acidbourbon/midi2cv/PCB/project.sch

## KiCad design PCB/project.sch (2016-03-10)

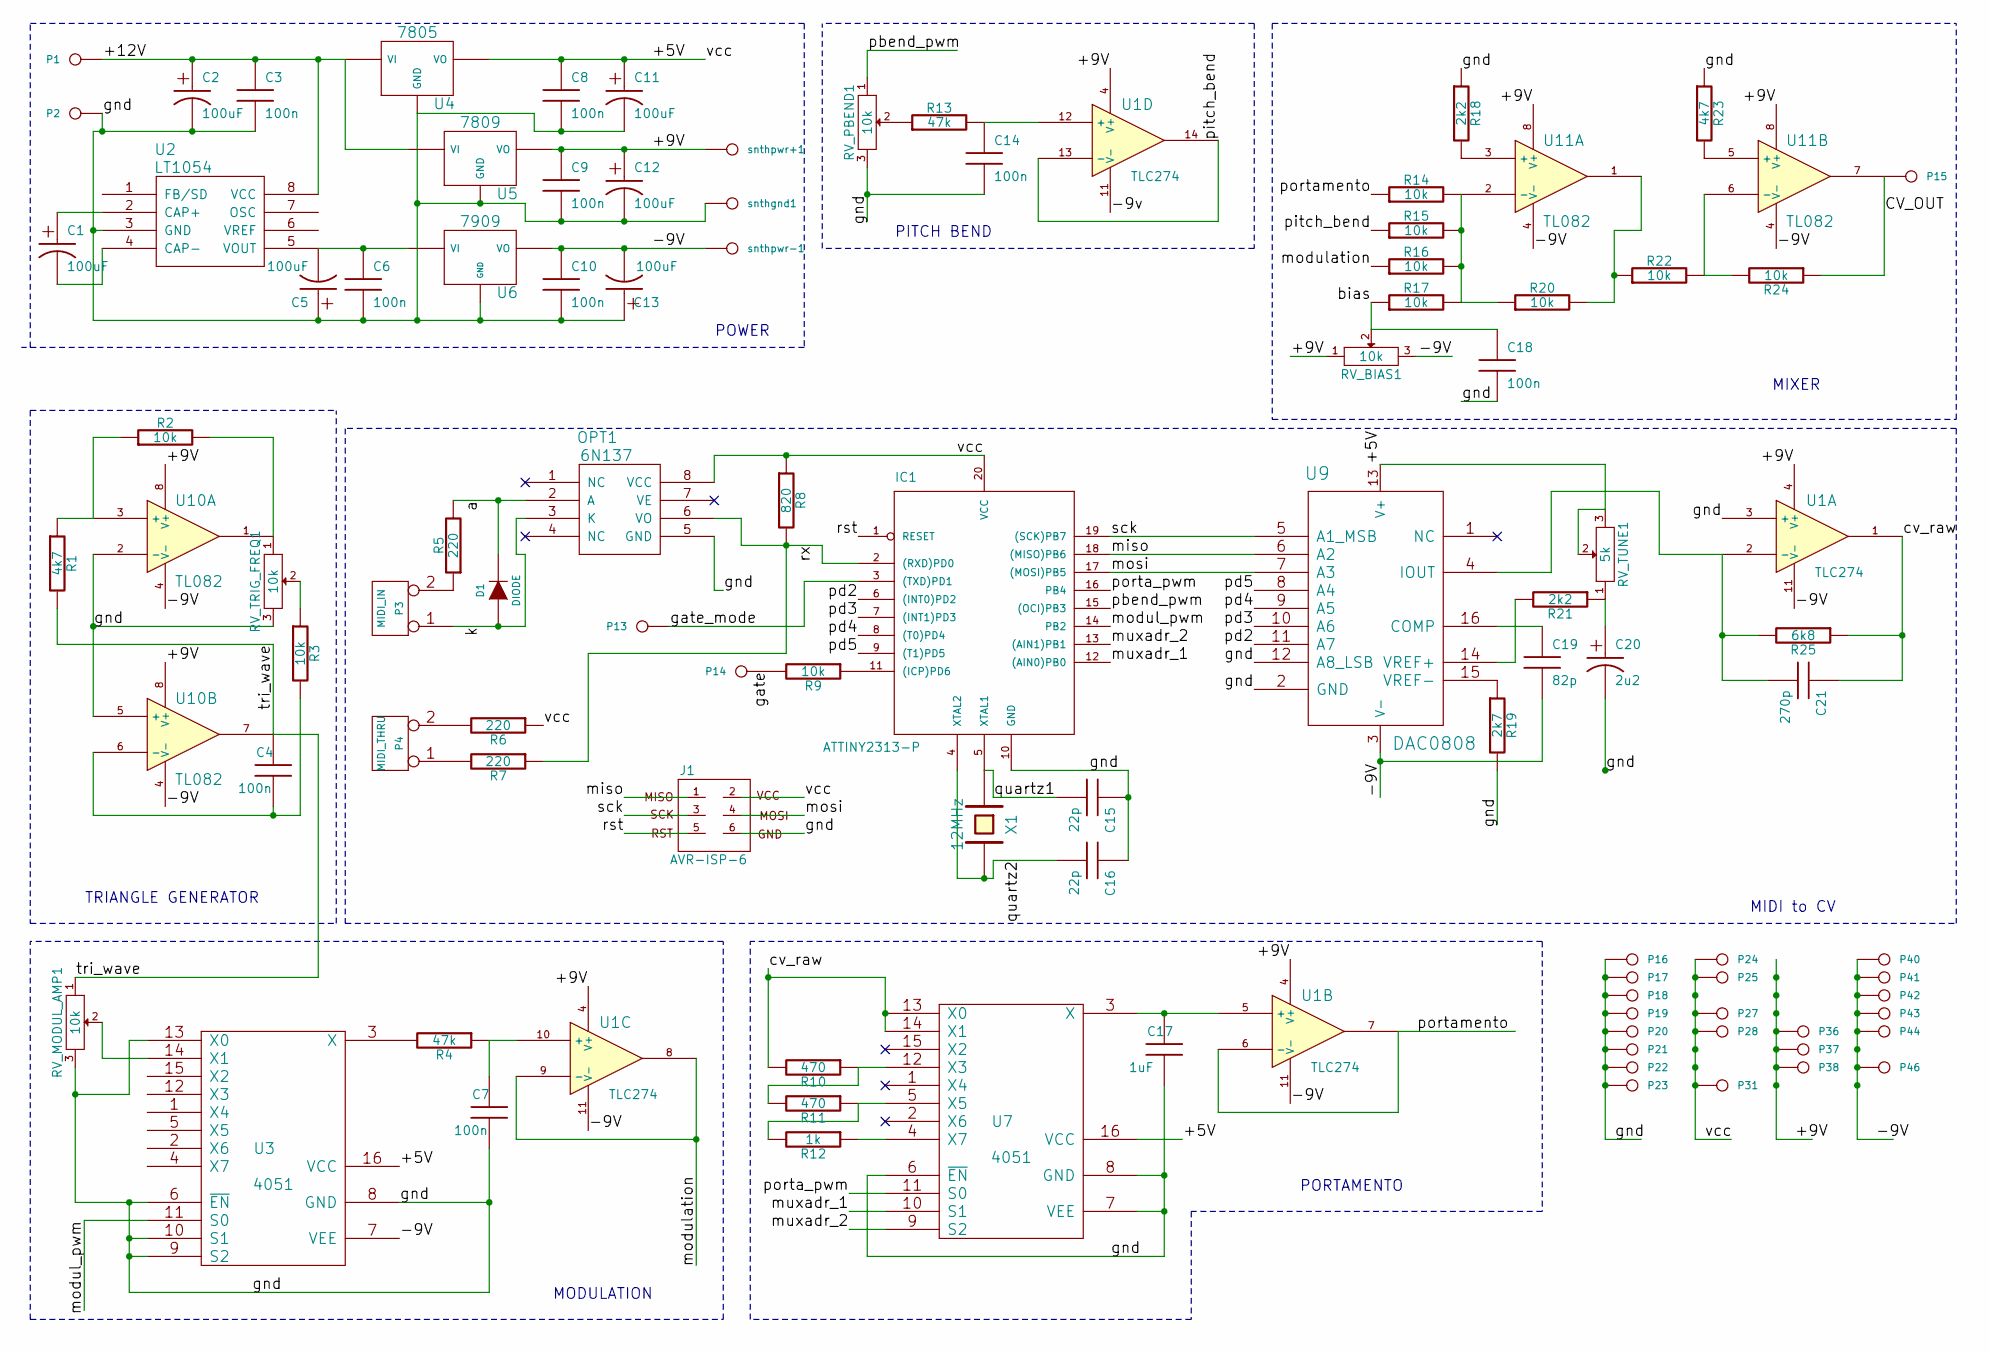
[picture p4: schematic project.sch]

Parts:
C1, C2, C5, C11, C12, C13: 100uF
C3, C4, C6, C7, C8, C9, C10, C14, C18: 100n
C15, C16: 22p
C17: 1uF
C19: 82p
C20: 2u2
C21: 270p
D1: DIODE
IC1: ATTINY2313-P; DIL20
J1: AVR-ISP-6
OPT1: 6N137
P1, P2, P13, P14, P15, P16, P17, P18, P19, P20, P21, P22, P23, P24, P25, P27, P28, P31, P36, P37, P38, P40, P41, P42, P43, P44, P46: CONN_1
P3: MIDI_IN
P4: MIDI_THRU
R1, R23: 4k7
R2, R3, R9, R14, R15, R16, R17, R20, R22, R24: 10k
R4, R13: 47k
R5, R6, R7: 220
R8: 820
R10, R11: 470
R12: 1k
R18, R21: 2k2
R19: 2k7
R25: 6k8
RV_BIAS1: 10k
RV_MODUL_AMP1: 10k
RV_PBEND1: 10k
RV_TRIG_FREQ1: 10k
RV_TUNE1: 5k
U1: TLC274
U2: LT1054
U3, U7: 4051
U4: 7805
U5: 7809
U6: 7909
U9: DAC0808
U10, U11: TL082
X1: 12MHz
snthgnd1: CONN_1
snthpwr+1: CONN_1
snthpwr-1: CONN_1

Connections:
+5V: C8.1, C11.1, IC1.20 (VCC), J1.2, OPT1.8 (VCC), P24.1, P25.1, P27.1, P28.1, P31.1, R6.1, R8.1, RV_TUNE1.2, RV_TUNE1.3, U3.16 (VCC), U4.VO, U7.16 (VCC), U9.13 (V+)
+9V: C9.1, C12.1, P36.1, P37.1, P38.1, RV_BIAS1.1, U1.4 (V+), U5.VO, U10.8 (V+), U11.8 (V+), snthpwr+1.1
+12V: C2.1, C3.1, P1.1, U2.8 (VCC), U4.VI, U5.VI
-9V: C10.1, C13.2, C19.2, P40.1, P41.1, P42.1, P43.1, P44.1, P46.1, RV_BIAS1.3, U1.11 (V-), U3.7 (VEE), U6.VO, U9.3 (V-), U10.4 (V-), U11.4 (V-), snthpwr-1.1
CV_OUT: P15.1, R24.1, U11.7
unnamed: C1.1, U2.2 (CAP+)
unnamed: C1.2, U2.4 (CAP-)
unnamed: C4.2, R3.2, U10.6 (-)
unnamed: C5.2, C6.1, U2.5 (VOUT), U6.VI
unnamed: C7.1, R4.1, U1.10 (+)
unnamed: C14.1, R13.2, U1.12 (+)
unnamed: C17.1, U1.5 (+), U7.3 (X)
unnamed: C19.1, U9.16 (COMP)
unnamed: C20.1, R21.1, RV_TUNE1.1
unnamed: C21.2, R25.2, U1.2 (-), U9.4 (IOUT)
unnamed: IC1.11 ((ICP)PD6), R9.1
unnamed: P3.2 (PM), R5.1
unnamed: P4.1, R7.2
unnamed: P4.2 (PM), R6.2
unnamed: R1.1, R2.1, U10.3 (+)
unnamed: R2.2, RV_TRIG_FREQ1.1, U10.1
unnamed: R3.1, RV_TRIG_FREQ1.2
unnamed: R4.2, U3.3 (X)
unnamed: R10.1, R11.2, U7.12 (X3)
unnamed: R11.1, R12.2, U7.5 (X5)
unnamed: R12.1, U7.4 (X7)
unnamed: R13.1, RV_PBEND1.2
unnamed: R14.2, R15.2, R16.2, R17.2, R20.1, U11.2 (-)
unnamed: R18.2, U11.3 (+)
unnamed: R19.1, U9.15 (VREF-)
unnamed: R20.2, R22.1, U11.1
unnamed: R21.2, U9.14 (VREF+)
unnamed: R22.2, R24.2, U11.6 (-)
unnamed: R23.2, U11.5 (+)
unnamed: RV_MODUL_AMP1.2, U3.14 (X1)
a: D1.2 (K), OPT1.2 (A), R5.2
bias: C18.1, R17.1, RV_BIAS1.2
cv_raw: C21.1, R10.2, R25.1, U1.1, U7.13 (X0), U7.14 (X1)
gate: P14.1, R9.2
gate_mode: IC1.3 ((TXD)PD1), P13.1
gnd: C2.2, C3.2, C5.1, C6.2, C7.2, C8.2, C9.2, C10.2, C11.2, C12.2, C13.1, C14.2, C15.1, C16.1, C17.2, C18.2, C20.2, IC1.10 (GND), J1.6, OPT1.5 (GND), P2.1, P16.1, P17.1, P18.1, P19.1, P20.1, P21.1, P22.1, P23.1, R18.1, R19.2, R23.1, RV_MODUL_AMP1.3, RV_PBEND1.3, RV_TRIG_FREQ1.3, U1.3 (+), U2.3 (GND), U3.6 (~EN), U3.8 (GND), U3.9 (S2), U3.10 (S1), U3.13 (X0), U4.GND, U5.GND, U6.GND, U7.6 (~EN), U7.7 (VEE), U7.8 (GND), U9.2 (GND), U9.12 (A8_LSB), U10.2 (-), U10.5 (+), snthgnd1.1
k: D1.1 (A), OPT1.3 (K), P3.1
miso: IC1.18 ((MISO)PB6), J1.1, U9.6 (A2)
modul_pwm: IC1.14 (PB2), U3.11 (S0)
modulation: R16.1, U1.8, U1.9 (-)
mosi: IC1.17 ((MOSI)PB5), J1.4, U9.7 (A3)
muxadr_1: IC1.12 ((AIN0)PB0), U7.10 (S1)
muxadr_2: IC1.13 ((AIN1)PB1), U7.9 (S2)
pbend_pwm: IC1.15 ((OCI)PB3), RV_PBEND1.1
pd2: IC1.6 ((INT0)PD2), U9.11 (A7)
pd3: IC1.7 ((INT1)PD3), U9.10 (A6)
pd4: IC1.8 ((T0)PD4), U9.9 (A5)
pd5: IC1.9 ((T1)PD5), U9.8 (A4)
pitch_bend: R15.1, U1.13 (-), U1.14
porta_pwm: IC1.16 (PB4), U7.11 (S0)
portamento: R14.1, U1.6 (-), U1.7
quartz1: C15.2, IC1.5 (XTAL1), X1.1
quartz2: C16.2, IC1.4 (XTAL2), X1.2
rst: IC1.1 (RESET), J1.5
rx: IC1.2 ((RXD)PD0), OPT1.6 (VO), R7.1, R8.2
sck: IC1.19 ((SCK)PB7), J1.3, U9.5 (A1_MSB)
tri_wave: C4.1, R1.2, RV_MODUL_AMP1.1, U10.7

Notes on the sheet:
PORTAMENTO
MODULATION
TRIANGLE GENERATOR
PITCH BEND
MIXER
MIDI to CV
POWER
